YUKESH0620/solarcore-4s-mppt-power-management-system/Images/Screenshot 2026-05-30 160942.png

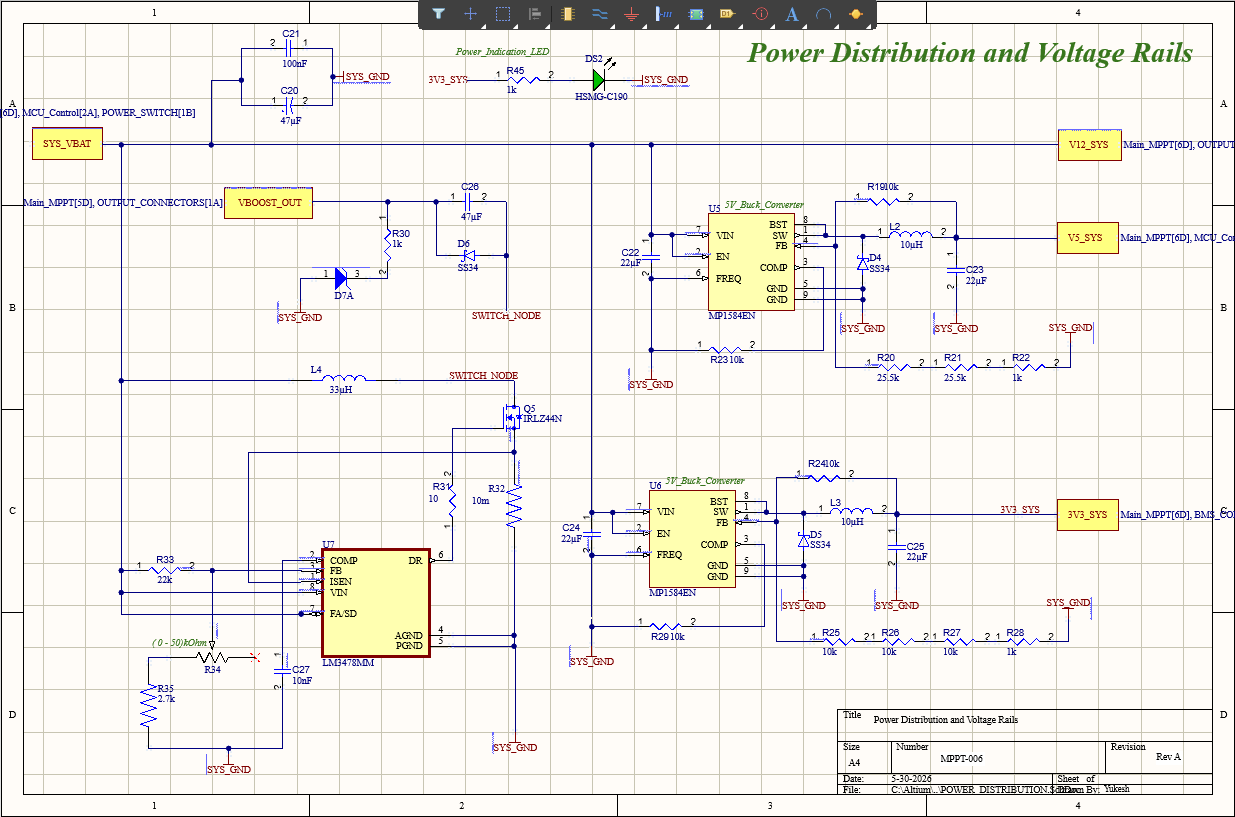
Images/Screenshot 2026-05-30 160942.png
