YUKESH0620/solarcore-4s-mppt-power-management-system/Firmware_v1/Drivers/oled_font.c

/*
 Project     : MPPT Solar Power Supply
 File        : oled_font.c

 Description :
 Standard 5x7 ASCII font table.

 Developer Notes :
 - Stores printable ASCII characters.
 - Used by SSD1306 driver.
 */

#include "oled_font.h"

const uint8_t Font5x7[][5] =
{
    /* Standard SSD1306 5x7 font table */
};
